simap/TapTDOA/firmware/controller/Src/testdata.c

#include <stdint.h>

const int sample_size = 6144;

const uint16_t sample1[] = {
        1941, 1940, 1941, 1940, 1941, 1942, 1941, 1942, 1941, 1941, 1941,
        1941, 1940, 1942, 1941, 1941, 1941, 1940, 1941, 1942, 1941, 1941,
        1940, 1941, 1941, 1942, 1941, 1940, 1941, 1941, 1941, 1943, 1942,
        1943, 1942, 1941, 1942, 1944, 1942, 1941, 1941, 1941, 1941, 1941,
        1942, 1941, 1942, 1941, 1941, 1942, 1941, 1940, 1941, 1942, 1940,
        1941, 1940, 1941, 1941, 1940, 1941, 1941, 1941, 1941, 1941, 1940,
        1941, 1941, 1940, 1941, 1941, 1941, 1942, 1942, 1942, 1942, 1941,
        1942, 1940, 1944, 1943, 1941, 1941, 1941, 1942, 1941, 1941, 1942,
        1940, 1940, 1939, 1940, 1942, 1943, 1941, 1941, 1941, 1940, 1941,
        1940, 1941, 1941, 1940, 1942, 1941, 1940, 1941, 1942, 1942, 1941,
        1941, 1942, 1942, 1941, 1941, 1942, 1942, 1940, 1941, 1942, 1941,
        1943, 1942, 1941, 1941, 1941, 1940, 1941, 1941, 1941, 1939, 1941,
        1942, 1941, 1941, 1942, 1942, 1941, 1941, 1940, 1941, 1942, 1940,
        1939, 1940, 1941, 1942, 1940, 1941, 1941, 1939, 1940, 1941, 1941,
        1941, 1940, 1940, 1941, 1942, 1943, 1942, 1941, 1941, 1942, 1941,
        1941, 1941, 1941, 1941, 1940, 1941, 1940, 1941, 1941, 1939, 1939,
        1940, 1939, 1939, 1939, 1939, 1939, 1941, 1941, 1941, 1941, 1940,
        1941, 1940, 1941, 1940, 1940, 1940, 1941, 1940, 1941, 1941, 1943,
        1942, 1942, 1942, 1941, 1941, 1941, 1941, 1942, 1942, 1941, 1942,
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
        1895, 1896, 1896, 1895, 1896, 1893, 1895, 1895, 1896, 1896, 1896,
        1896, 1896, 1897, 1897, 1896, 1896, 1898, 1897, 1898, 1898, 1898,
        1899, 1897, 1898, 1898, 1896, 1897, 1897, 1896, 1898, 1895, 1896,
        1896, 1896, 1896, 1897, 1895, 1897, 1896, 1895, 1895, 1895, 1896,
        1896, 1895, 1896, 1895, 1895, 1897, 1896, 1897, 1897, 1895, 1897,
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
};
